BoujeeEnjinia1701/voidscope/cad/drawings/VDS-DWG-001.pdf

CONCEPT, NOT FOR FABRICATION | VoidScope · github.com/BoujeeEnjinia1701/voidscope

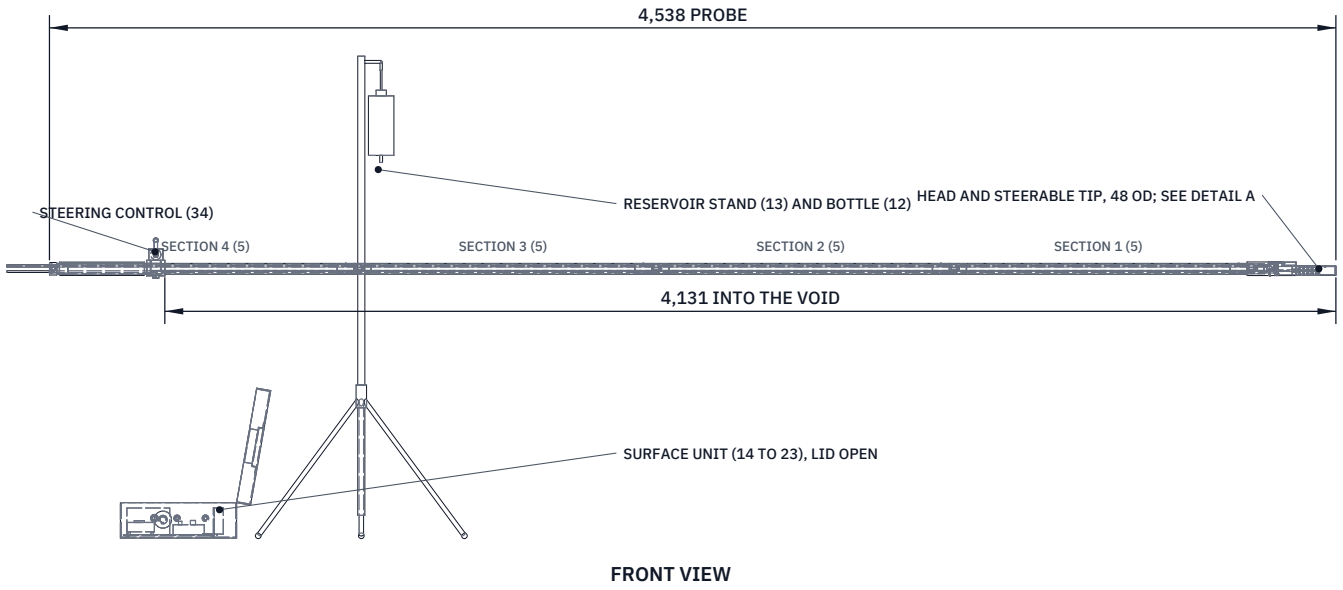
[picture p47: figure]
FRONT VIEW; 4,538 PROBE; 4,131 INTO THE VOID; STEERING CONTROL (34); SECTION 4 (5); SECTION 3 (5); SECTION 2 (5); SECTION 1 (5); SURFACE UNIT (14 TO 23), LID OPEN; RESERVOIR STAND (13) AND BOTTLE (12)

Scale 1:25; looking at the front (along +Y)

TOP VIEW
Scale 1:25; looking down (along -Z)

RIGHT VIEW
Scale 1:25; looking at the right side (along -X)

4688

1098 1702

HEAD AND STEERABLE TIP, 48 OD; SEE DETAIL A

TAIL CAP AND AIR INLET (7); GRIP (8)

OPERATOR STANDS BEHIND THE TAIL CAP (-X); TIP POINTS +X

ISOMETRIC VIEW
Not to scale; seen from the front right and above, about 30 deg elevation

DETAIL A: HEAD AND STEERABLE TIP
Scale 1:2.5; plan from above, tip to the right, straight; bends 90 deg each way in this plane

MAIN DIMENSIONS AND INTERFACES (MM)
Probe 4,538 long; working length 4,131; axis 950 above ground as held Rod: 4 sections 38.1 x 1.47 6061-T6 tube, 1,050 long
Couplers 34.93 x 2.11 x 120, 60 bonded and pinned; snap button Head 48 OD at most, tip straight; passes a 51 mm core hole (R1) Collar: socket, plenum, 6 x 5 outlets, speaker, water exit
Nose: base link 6.5 below the axis; bite valve on top
Tip: 5 joints, 90 deg each way; 140 long; 29 mm IP68 camera Steering: lever and drum on section 4, two wires in housings Air: rod bore is the duct; inlet barb on the tail cap
Water: 4 x 2.5 tube inside an 8 x 6 PTFE guide
Case 410 x 330 x 175; lid opened 100 deg
Third-angle; front view from -Y; (n) = BOM line
REV | DESCRIPTION | DATE | BY
P1 | Preliminary GA for TRL 3 (from cad/src/model.py) | 2026-10-03 | AC
P2 | VDS-DDR-002: design for construction | 2026-10-03 | AC
P3 | VDS-DDR-003: steerable camera tip and steering control | 2026-10-03 | AC
VOIDSCOPE | github.com/BoujeeEnjinia1701/voidscope

## Rubble void search probe and surface unit: general arrangement

DRAWING NO.
VDS-DWG-001

REV
P3

SHEET
1 of 1

SIZE

## ANSI B

SCALE
1:25

UNITS
mm
PROJECTION | DATE
2026-10-03

DRAWN
Amish Chadha

MATERIAL / NOTES
6061-T6 aluminium tube and bar; bought parts per bom/bom.csv. PRELIMINARY, NOT FOR FABRICATION
Licensed CERN-OHL-S-2.0 · Design Molecule Lab · designmolecule.com | Generated from cad/src; do not edit by hand
