BoujeeEnjinia1701/voidscope/cad/drawings/VDS-DWG-101.pdf

### BUILD PLAN SKETCH, PLAN NOT YET BUILT VoidScope · github.com/BoujeeEnjinia1701/voidscope

FRONT VIEW
Scale 1:5; looking at the front (along +Y)

TOP VIEW
Scale 1:5; looking down (along -Z)

RIGHT VIEW
Scale 1:5; looking at the right side (along -X)

1050

38 38

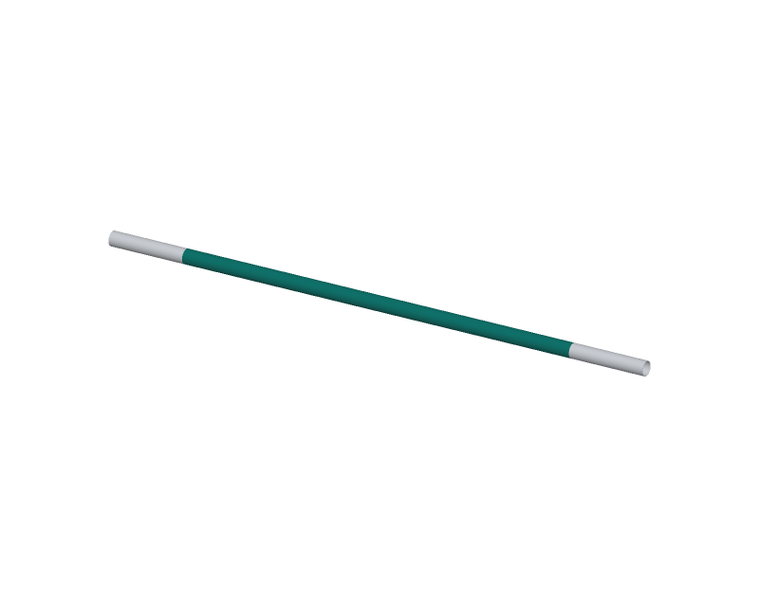
[picture p48: figure]

WHERE IT GOES
This part in colour, its neighbours in grey

HOW TO MAKE IT AND HOW IT FITS
Make four. Cut 1,050 mm, square, from 38.1 x 1.47 mm tube. Deburr inside and out; the inside edge must not cut the cable. Scribe a straight line along the tube: the button line (+Y). Back end, sections 1 to 3: drill 8.5 mm on the button line,
30 mm from the end. This takes the next section's button.

Back end, section 4: no button hole; the tail cap pins go in 4.0 mm holes top and bottom, 20 mm from the end (step 2); two 4 mm housing holes on top, 10.5 mm off centre,
332 and 368 mm from the back end.
Front end: the coupler pin holes, 4.0 mm top and bottom 30 mm from the end, are drilled through with the coupler fitted.
Depth marks every 100 mm from the tip, section number at each end, paint marker under clear heat-shrink.
Check: the next coupler slides in by hand with no rock.
REV | DESCRIPTION | DATE | BY
P1 | Making sketch for the prototype build plan | 2026-10-03 | AC
P2 | VDS-DDR-003: steerable camera tip | 2026-10-03 | AC
VOIDSCOPE | github.com/BoujeeEnjinia1701/voidscope

## VoidScope rod section (make 4): making sketch

DRAWING NO.
VDS-DWG-101

REV
P2

SHEET
1 of 1

SIZE

## ANSI B

SCALE
1:5

UNITS
mm
PROJECTION | DATE
2026-10-03

DRAWN
Amish Chadha

MATERIAL / NOTES
6061-T6 drawn tube 38.1 x 1.47 mm (1.5 x 0.058 in)
Licensed CERN-OHL-S-2.0 · Design Molecule Lab · designmolecule.com | Generated from cad/src; do not edit by hand
