BoujeeEnjinia1701/voidscope/cad/drawings/VDS-DWG-102.pdf

### BUILD PLAN SKETCH, PLAN NOT YET BUILT VoidScope · github.com/BoujeeEnjinia1701/voidscope

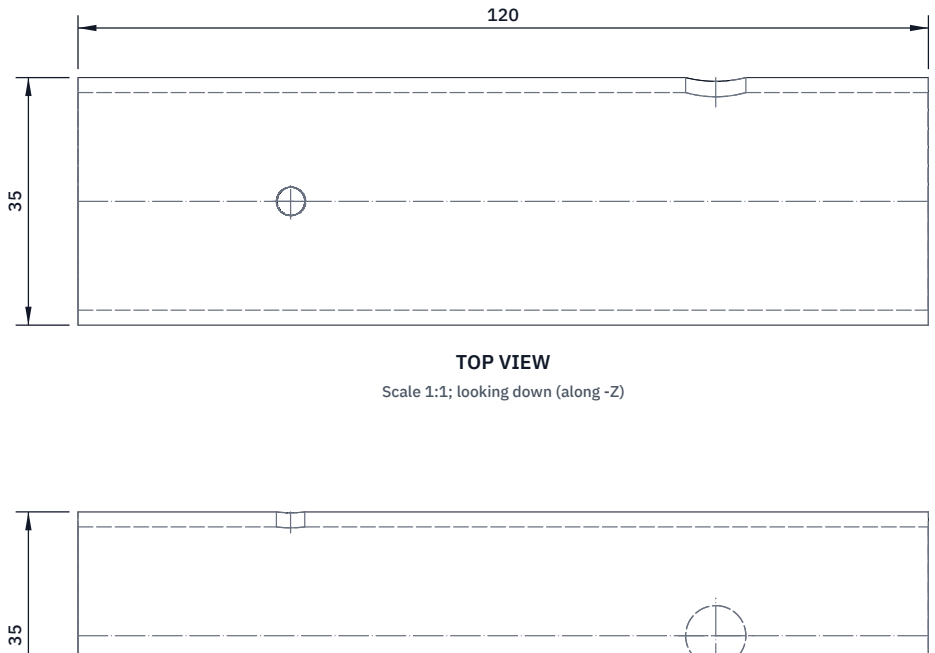
[picture p49: figure]
TOP VIEW; Scale 1:1; looking down (along -Z)

FRONT VIEW
Scale 1:1; looking at the front (along +Y)

RIGHT VIEW
Scale 1:1; looking at the right side (along -X)

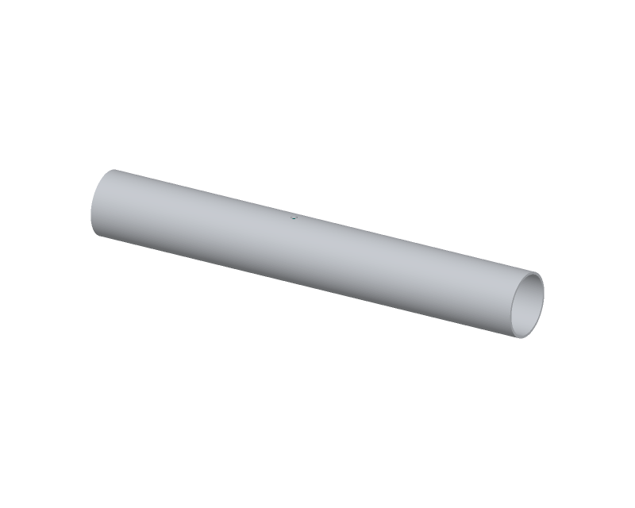
[picture p50: figure]

WHERE IT GOES
This part in colour, its neighbours in grey

HOW TO MAKE IT AND HOW IT FITS
Make four. Cut 120 mm from 34.93 x 2.11 mm tube; deburr. Chamfer the outside of one end 1 mm x 45 deg: the free end. Drill 8.5 mm for the snap button 30 mm from the free end. Fit the V-spring button from inside, button out through
the hole. Spring legs lie flat across the bore (top to
bottom stays clear for the cable and guide tube).
Bond: the plain end goes 60 mm into the section's front end with structural epoxy, button on the section's button line. Drill 4.0 mm through tube and coupler, top and bottom, 30 mm from the section end; press in the pins flush both sides.
Fit: 0.11 mm a side in the next tube; it must slide freely. Check: pull hard by hand; nothing moves; button pops fully.
REV | DESCRIPTION | DATE | BY
P1 | Making sketch for the prototype build plan | 2026-10-03 | AC
VOIDSCOPE | github.com/BoujeeEnjinia1701/voidscope

## VoidScope coupler (make 4): making sketch

DRAWING NO.
VDS-DWG-102

REV
P1

SHEET
1 of 1

SIZE

## ANSI B

SCALE
1:1

UNITS
mm
PROJECTION | DATE
2026-10-03

DRAWN
Amish Chadha

MATERIAL / NOTES
6061-T6 drawn tube 34.93 x 2.11 mm (1.375 x 0.083 in)
Licensed CERN-OHL-S-2.0 · Design Molecule Lab · designmolecule.com | Generated from cad/src; do not edit by hand
