BoujeeEnjinia1701/voidscope/cad/drawings/VDS-DWG-103.pdf

### BUILD PLAN SKETCH, PLAN NOT YET BUILT VoidScope · github.com/BoujeeEnjinia1701/voidscope

FRONT VIEW
Scale 1:1; looking at the front (along +Y)

TOP VIEW
Scale 1:1; looking down (along -Z)

RIGHT VIEW
Scale 1:1; looking at the right side (along -X)

75

48 48

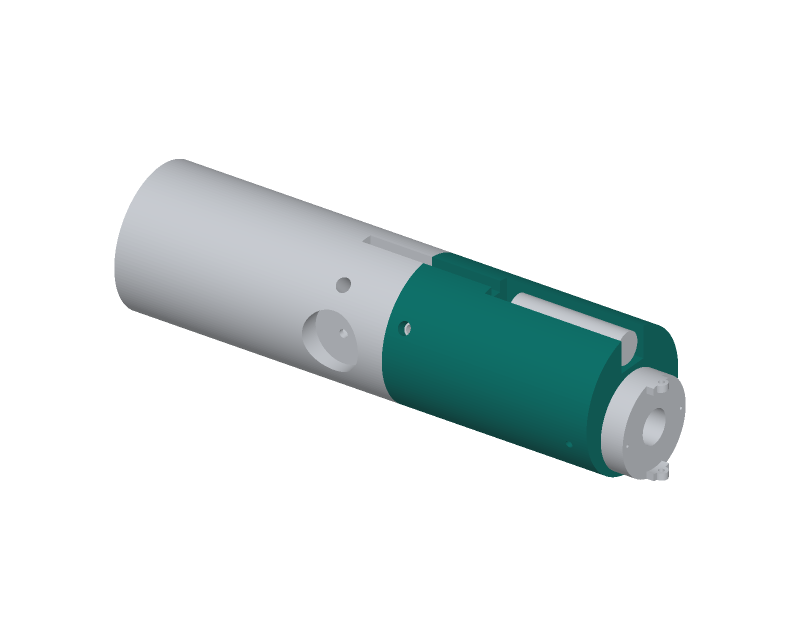
[picture p51: figure]

WHERE IT GOES
This part in colour, its neighbours in grey

HOW TO MAKE IT AND HOW IT FITS
Lathe: face and turn to 48 mm outside, 75 mm long.
Back end: bore 40.2 mm, 12 mm deep, for the collar spigot. Offset the work 6.5 mm (4-jaw chuck): bore 29.3 mm from 12 mm right through the front, for the base link of the steerable tip. Thinnest wall 2.85 mm, at the bottom.
Mill or saw and file on top: pocket 11.5 mm wide, floor
12 mm above the axis, 50 mm back from the front face. Groove on top 4.5 mm wide, floor 20 mm above the axis, from the back face to the pocket (breaks into the bore). Three 4.5 mm holes 6 mm from the back face, at 30, 150 and 270 deg from the side; countersink for M4.
Two M3 tapped holes, 7 mm from the front, either side on the bore's centre height, for the base link grub screws. Break edges 0.5 mm. Check: base link spigot slides in.
REV | DESCRIPTION | DATE | BY
P1 | Making sketch for the prototype build plan | 2026-10-03 | AC
P2 | VDS-DDR-003: steerable camera tip | 2026-10-03 | AC
VOIDSCOPE | github.com/BoujeeEnjinia1701/voidscope

## VoidScope nose: making sketch

DRAWING NO.
VDS-DWG-103

REV
P2

SHEET
1 of 1

SIZE

## ANSI B

SCALE
1:1

UNITS
mm
PROJECTION | DATE
2026-10-03

DRAWN
Amish Chadha

MATERIAL / NOTES
6061-T6 round bar 50 mm, 80 mm long
Licensed CERN-OHL-S-2.0 · Design Molecule Lab · designmolecule.com | Generated from cad/src; do not edit by hand
