BoujeeEnjinia1701/voidscope/cad/drawings/VDS-DWG-104.pdf

### BUILD PLAN SKETCH, PLAN NOT YET BUILT VoidScope · github.com/BoujeeEnjinia1701/voidscope

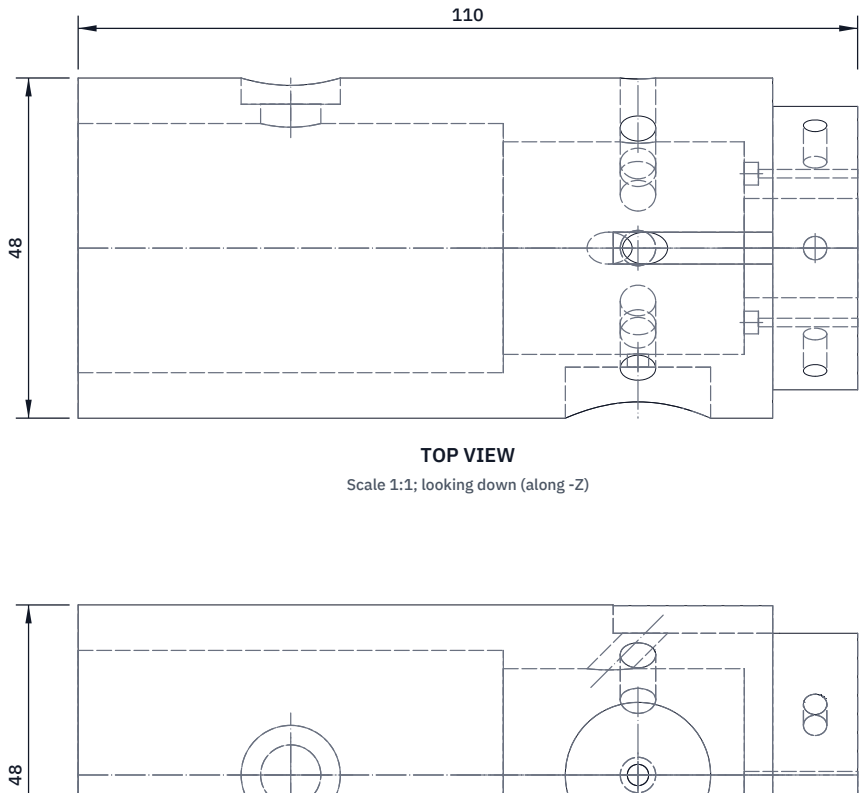
[picture p52: figure]
TOP VIEW; Scale 1:1; looking down (along -Z)
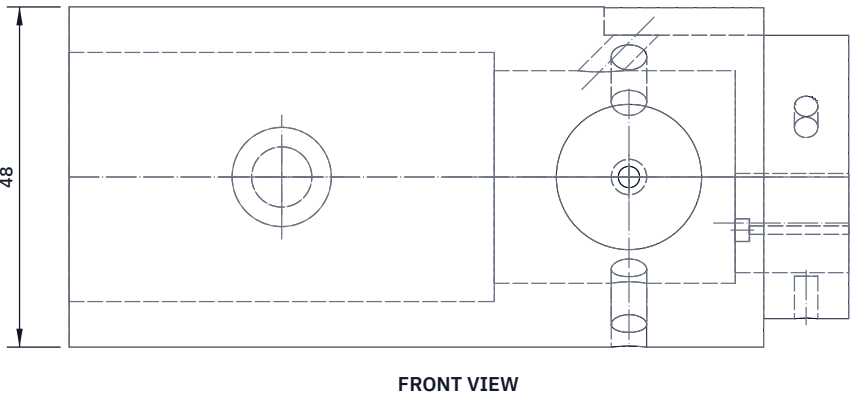
[picture p53: figure]
FRONT VIEW

Scale 1:1; looking at the front (along +Y)

RIGHT VIEW
Scale 1:1; looking at the right side (along -X)

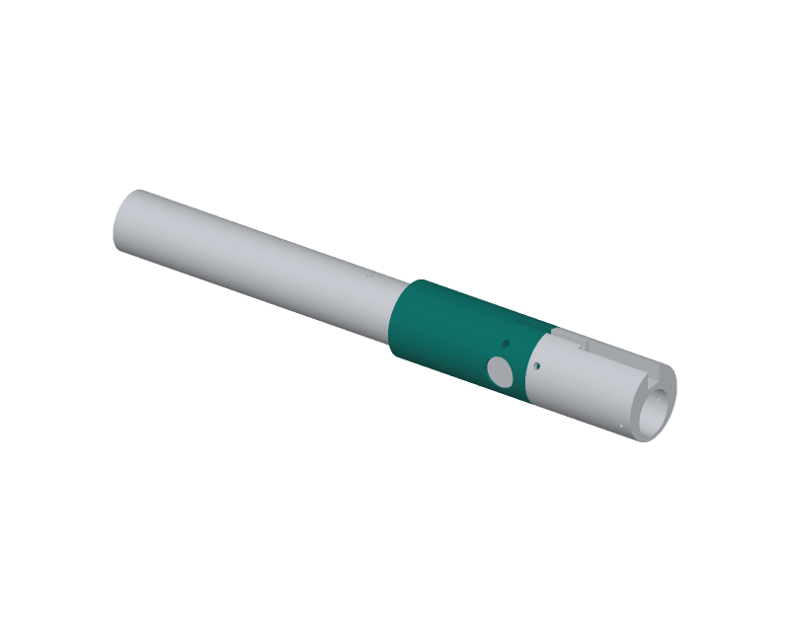
[picture p54: figure]

WHERE IT GOES
This part in colour, its neighbours in grey

HOW TO MAKE IT AND HOW IT FITS
Lathe: 48 mm outside x 98 mm, then a 40 mm spigot 12 long. Back: bore 35.16 mm, 60 deep (a coupler must slide in).
Bore 30 mm from 60 to 94 mm: the air plenum; 4 mm front wall. Spigot: 14 mm bore 6.5 mm below the axis, through, for the cable grommet. Tap three M4 holes 6 mm deep, 4 from its end. Button hole 8.5 mm on the button line, 30 mm from the back; spotface 14 mm down to 20.3 mm from the axis.
Six 5 mm outlets 79 mm from the back face, at 0, 45, 135, 240, 270 and 300 deg from the button line toward the top. Steering: two 3.2 mm stops 2 deep in the plenum side of the front wall, 10.5 mm each side, 7.5 below the axis; 1.2 mm wire holes on through the spigot.
Speaker pocket on the far side: 20.5 mm, flat floor 16.8 mm from the axis, 79 mm back; 3 mm wire hole into the plenum. Water exit 4.5 mm at 45 deg on top, axis crossing 12 mm above the axis 72 mm from the back; groove 4.5 x 4 on top. Check: coupler, nose, speaker fit; blow through outlets.
REV | DESCRIPTION | DATE | BY
P1 | Making sketch for the prototype build plan | 2026-10-03 | AC
P2 | VDS-DDR-003: steerable camera tip | 2026-10-03 | AC
VOIDSCOPE | github.com/BoujeeEnjinia1701/voidscope

## VoidScope collar: making sketch

DRAWING NO.
VDS-DWG-104

REV
P2

SHEET
1 of 1

SIZE

## ANSI B

SCALE
1:1

UNITS
mm
PROJECTION | DATE
2026-10-03

DRAWN
Amish Chadha

MATERIAL / NOTES
6061-T6 round bar 50 mm, 115 mm long
Licensed CERN-OHL-S-2.0 · Design Molecule Lab · designmolecule.com | Generated from cad/src; do not edit by hand
