BoujeeEnjinia1701/voidscope/cad/drawings/VDS-DWG-105.pdf

### BUILD PLAN SKETCH, PLAN NOT YET BUILT VoidScope · github.com/BoujeeEnjinia1701/voidscope

FRONT VIEW
Scale 1:1; looking at the front (along +Y)

TOP VIEW
Scale 1:1; looking down (along -Z)

RIGHT VIEW
Scale 1:1; looking at the right side (along -X)

65

44 44

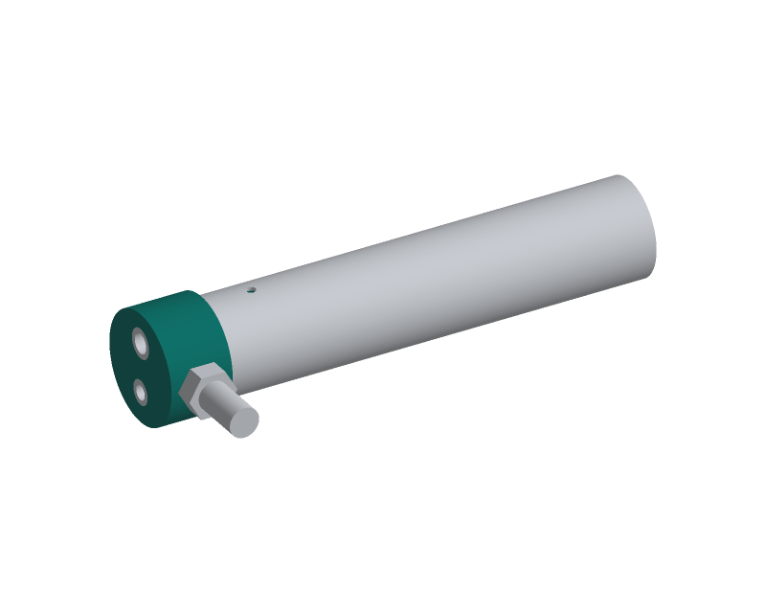
[picture p55: figure]

WHERE IT GOES
This part in colour, its neighbours in grey

HOW TO MAKE IT AND HOW IT FITS
Lathe: flange 44 mm outside x 25 mm; plug 35.0 mm x 40 mm (0.08 mm a side in the rod: bonded, not a slide fit).
Bore 30 mm from the plug end to 8 mm from the back face. End wall: 10 mm hole 10 mm below the axis (cable) and
12 mm hole 10 mm above it (guide tube); deburr; grommets. Side of the flange, away from the button line: drill and
tap 1/4 BSP 12.5 mm from the back face into the bore. Pins: drill 4.0 mm top and bottom through rod and plug
20 mm in front of the flange after bonding (step 2). Check: plug enters the rod fully; barb seals with tape.
REV | DESCRIPTION | DATE | BY
P1 | Making sketch for the prototype build plan | 2026-10-03 | AC
VOIDSCOPE | github.com/BoujeeEnjinia1701/voidscope

## VoidScope tail cap: making sketch

DRAWING NO.
VDS-DWG-105

REV
P1

SHEET
1 of 1

SIZE

## ANSI B

SCALE
1:1

UNITS
mm
PROJECTION | DATE
2026-10-03

DRAWN
Amish Chadha

MATERIAL / NOTES
6061-T6 round bar 50 mm, 70 mm long
Licensed CERN-OHL-S-2.0 · Design Molecule Lab · designmolecule.com | Generated from cad/src; do not edit by hand
