BoujeeEnjinia1701/voidscope/cad/drawings/VDS-DWG-106.pdf

### BUILD PLAN SKETCH, PLAN NOT YET BUILT VoidScope · github.com/BoujeeEnjinia1701/voidscope

FRONT VIEW
Scale 1:5; looking at the front (along +Y)

TOP VIEW
Scale 1:5; looking down (along -Z)

RIGHT VIEW
Scale 1:5; looking at the right side (along -X)

330

300 3

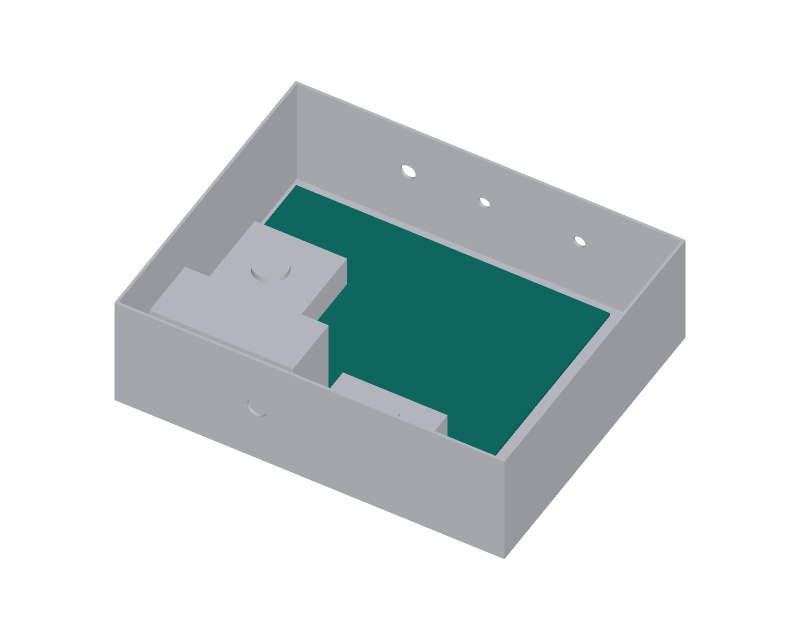
[picture p56: figure]

WHERE IT GOES
This part in colour, its neighbours in grey

HOW TO MAKE IT AND HOW IT FITS
Cut 330 x 300 mm from 3 mm sheet; round corners 5 mm. Corner holes 5.5 mm, 15 mm in from each edge: the four spacers and M5 screws through the case floor.
Mark the parts from the corner nearest the case's -X, -Y corner: battery at 12, 12 (151 x 65); strap slots 4 x 25 mm each side of it; blower at 12, 110 on four standoffs; modules tray at 175, 12; flow meter angle at 280, 230. Drill each fixing to suit the part as bought (M3 or M4). Deburr; no sharp edge near the battery leads.
Check: lay every part on the plate before drilling.
REV | DESCRIPTION | DATE | BY
P1 | Making sketch for the prototype build plan | 2026-10-03 | AC
VOIDSCOPE | github.com/BoujeeEnjinia1701/voidscope

## VoidScope equipment plate: making sketch

DRAWING NO.
VDS-DWG-106

REV
P1

SHEET
1 of 1

SIZE

## ANSI B

SCALE
1:5

UNITS
mm
PROJECTION | DATE
2026-10-03

DRAWN
Amish Chadha

MATERIAL / NOTES
5052 aluminium sheet 3 mm
Licensed CERN-OHL-S-2.0 · Design Molecule Lab · designmolecule.com | Generated from cad/src; do not edit by hand
