BoujeeEnjinia1701/voidscope/cad/drawings/VDS-DWG-108.pdf

### BUILD PLAN SKETCH, PLAN NOT YET BUILT VoidScope · github.com/BoujeeEnjinia1701/voidscope

FRONT VIEW
Scale 1:5; looking at the front (along +Y)

TOP VIEW
Scale 1:5; looking down (along -Z)

RIGHT VIEW
Scale 1:5; looking at the right side (along -X)

410

330 125

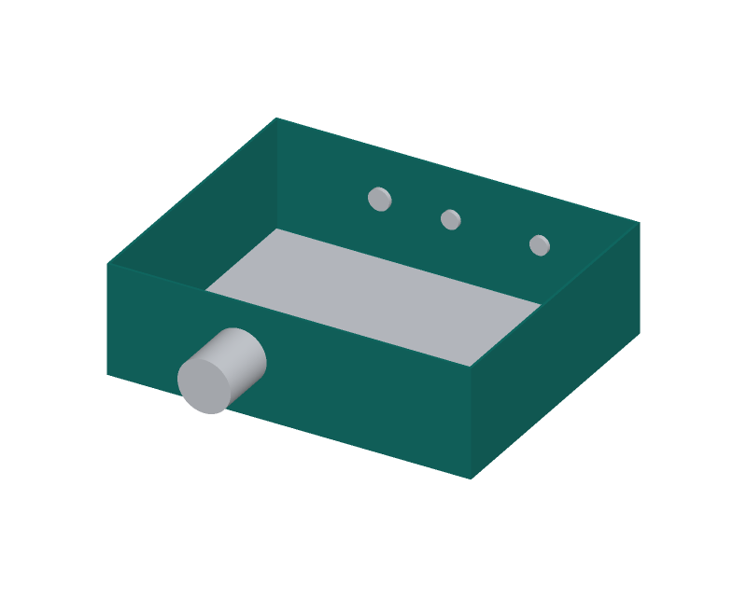
[picture p57: figure]

WHERE IT GOES
This part in colour, its neighbours in grey

HOW TO MAKE IT AND HOW IT FITS
Bought case 410 x 330 x 175 mm; drill the base only as here. Wall toward the probe (the +Y long side), 70 mm up from the floor outside: 16 mm for the camera socket 120 mm from the left end; 12 mm for the headset socket at 200 mm; 12.5 mm for the air outlet bulkhead at 300 mm.
Opposite wall: 21 mm for the intake filter, 150 mm from the left end, 65 mm up.
Floor: four 5.5 mm holes matching the plate's corner holes. Lid: four 5.5 mm holes for the monitor bracket feet.
Use a step drill, slow; deburr; every hole gets its seal. Check: the case still closes and latches.
REV | DESCRIPTION | DATE | BY
P1 | Making sketch for the prototype build plan | 2026-10-03 | AC
VOIDSCOPE | github.com/BoujeeEnjinia1701/voidscope

## VoidScope surface unit case: drilling sketch

DRAWING NO.
VDS-DWG-108

REV
P1

SHEET
1 of 1

SIZE

## ANSI B

SCALE
1:5

UNITS
mm
PROJECTION | DATE
2026-10-03

DRAWN
Amish Chadha

MATERIAL / NOTES
Bought IP67 case, polypropylene
Licensed CERN-OHL-S-2.0 · Design Molecule Lab · designmolecule.com | Generated from cad/src; do not edit by hand
