BoujeeEnjinia1701/voidscope/cad/drawings/VDS-DWG-110.pdf

### BUILD PLAN SKETCH, PLAN NOT YET BUILT VoidScope · github.com/BoujeeEnjinia1701/voidscope

FRONT VIEW
Scale 2:1; looking at the front (along +Y)

TOP VIEW
Scale 2:1; looking down (along -Z)

RIGHT VIEW
Scale 2:1; looking at the right side (along -X)

20

33 33

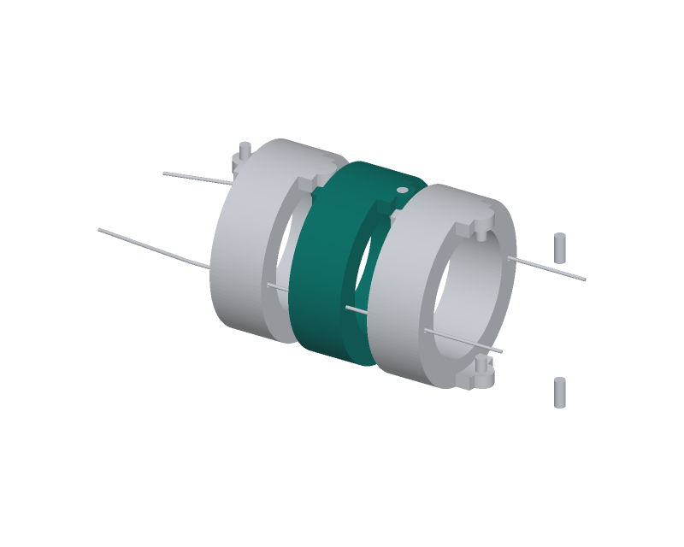
[picture p58: figure]

WHERE IT GOES
This part in colour, its neighbours in grey

HOW TO MAKE IT AND HOW IT FITS
Make four by laser sintering in PA12 from the model; any online print service. No supports needed.
Body 33 mm outside, 23 mm bore, 10 mm long. Back: inner lugs 8 mm wide, top and bottom, 11.5 to 13.9 mm from the centre. Front: outer lugs, 14.1 to 16.5 mm. Lug ends are rounded about the pin.
Pin holes 2.0 mm (ream after printing), 2.6 mm from each lug's root face, top and bottom.
Wire holes 1.2 mm on the two sides, 14 mm from the centre; run a 1.2 mm drill through each.
The faces close at 18 deg: that is the joint's stop.
Check: two links pin together and swing 18 deg each way.
REV | DESCRIPTION | DATE | BY
P1 | Making sketch for the prototype build plan | 2026-10-03 | AC
VOIDSCOPE | github.com/BoujeeEnjinia1701/voidscope

## VoidScope bending link (make 4): making sketch

DRAWING NO.
VDS-DWG-110

REV
P1

SHEET
1 of 1

SIZE

## ANSI B

SCALE
2:1

UNITS
mm
PROJECTION | DATE
2026-10-03

DRAWN
Amish Chadha

MATERIAL / NOTES
PA12 nylon, laser sintered (SLS)
Licensed CERN-OHL-S-2.0 · Design Molecule Lab · designmolecule.com | Generated from cad/src; do not edit by hand
