BoujeeEnjinia1701/voidscope/cad/drawings/VDS-DWG-111.pdf

### BUILD PLAN SKETCH, PLAN NOT YET BUILT VoidScope · github.com/BoujeeEnjinia1701/voidscope

FRONT VIEW
Scale 2:1; looking at the front (along +Y)

TOP VIEW
Scale 2:1; looking down (along -Z)

RIGHT VIEW
Scale 2:1; looking at the right side (along -X)

27

33 33

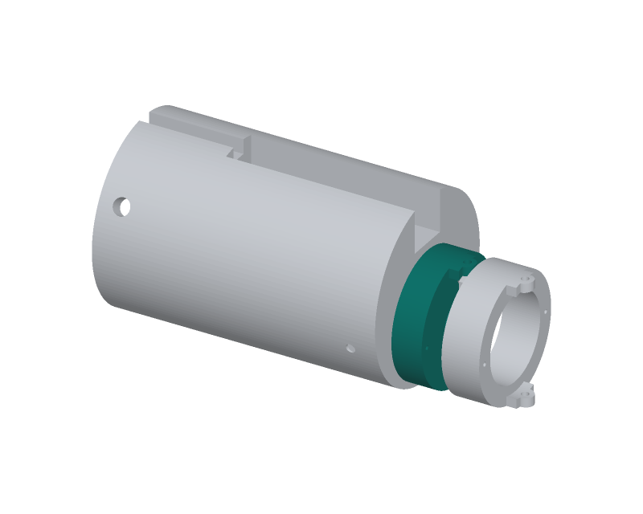
[picture p59: figure]

WHERE IT GOES
This part in colour, its neighbours in grey

HOW TO MAKE IT AND HOW IT FITS
Lathe: 29.25 mm spigot 14 mm long, 33 mm flange 8 mm, 12 mm bore through. The spigot is a close slide fit in
the nose's 29.3 mm bore.
Front: leave a 4.9 mm stub at 33 mm outside; mill it
away to two outer lugs, 8 mm wide, top and bottom, outside 14.1 mm from the centre; round the lug ends. Drill 2.0 mm pin holes 2.6 mm ahead of the flange face. Wire holes 1.2 mm, drilled on a slant: from 10.5 mm out
and 1 mm low at the back face to 14 mm out on the
centre line at the flange front (a drill jig helps).
Two dimples 1.5 mm deep, 7 mm from the spigot's front end, on the sides, for the M3 grub screws in the nose.
REV | DESCRIPTION | DATE | BY
P1 | Making sketch for the prototype build plan | 2026-10-03 | AC
VOIDSCOPE | github.com/BoujeeEnjinia1701/voidscope

## VoidScope base link: making sketch

DRAWING NO.
VDS-DWG-111

REV
P1

SHEET
1 of 1

SIZE

## ANSI B

SCALE
2:1

UNITS
mm
PROJECTION | DATE
2026-10-03

DRAWN
Amish Chadha

MATERIAL / NOTES
6061-T6 round bar 35 mm, 25 mm long
Licensed CERN-OHL-S-2.0 · Design Molecule Lab · designmolecule.com | Generated from cad/src; do not edit by hand
