BoujeeEnjinia1701/voidscope/cad/drawings/VDS-DWG-112.pdf

### BUILD PLAN SKETCH, PLAN NOT YET BUILT VoidScope · github.com/BoujeeEnjinia1701/voidscope

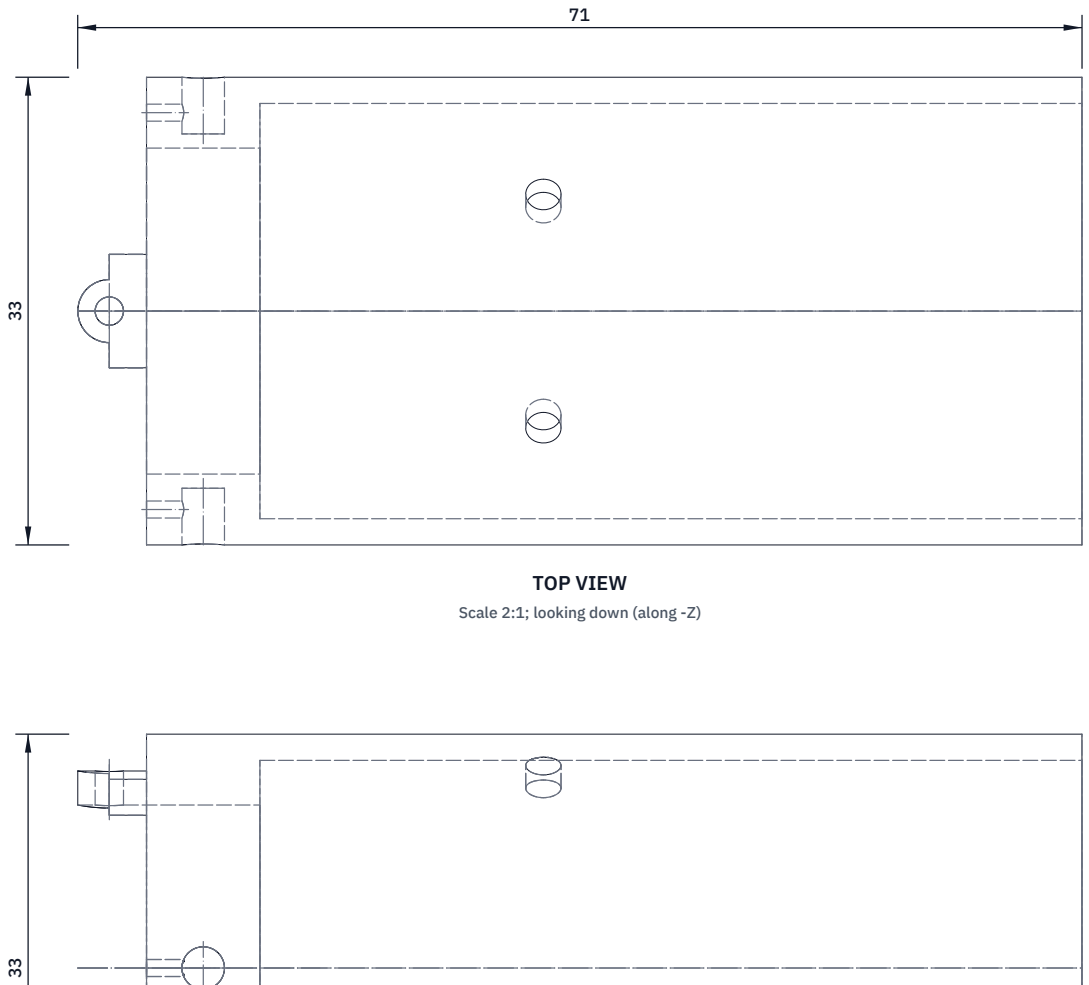
[picture p60: figure]
TOP VIEW; Scale 2:1; looking down (along -Z)
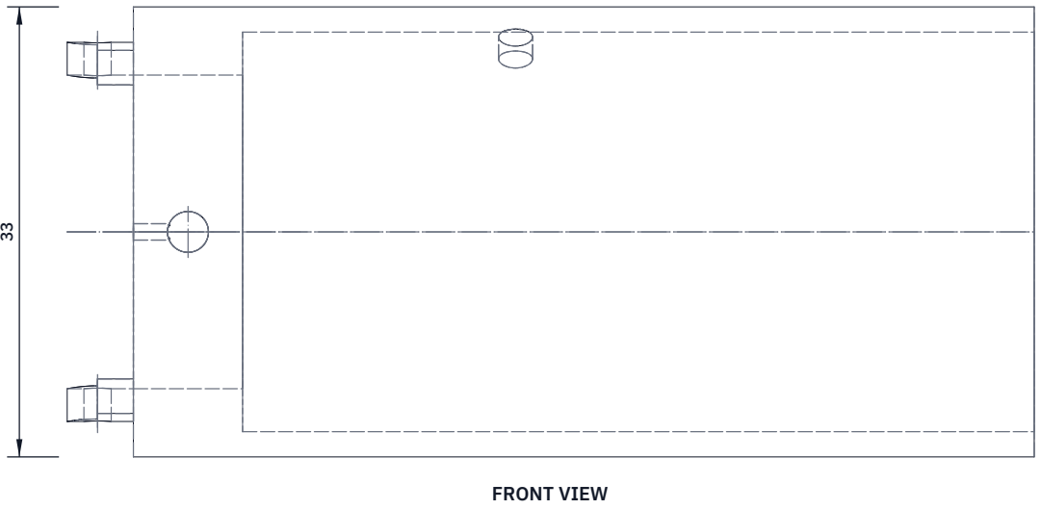
[picture p61: figure]
FRONT VIEW

Scale 2:1; looking at the front (along +Y)

RIGHT VIEW
Scale 2:1; looking at the right side (along -X)

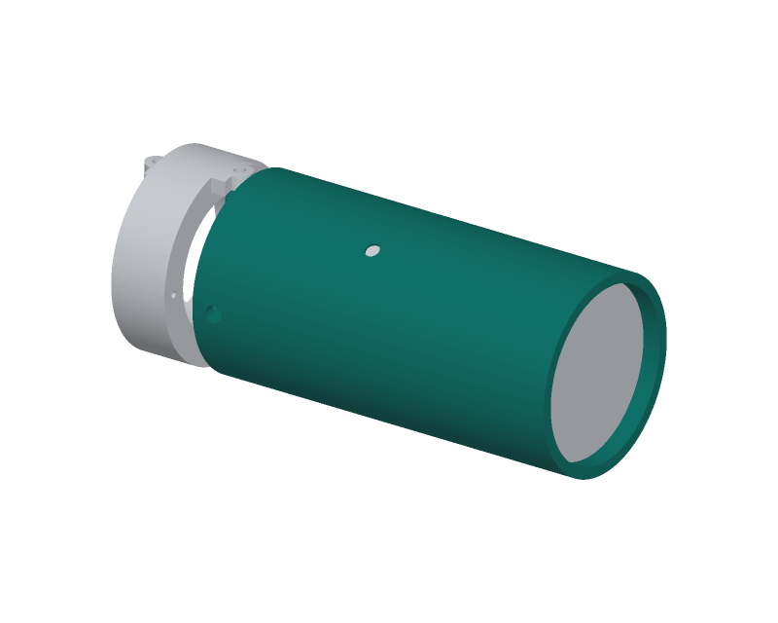
[picture p62: figure]

WHERE IT GOES
This part in colour, its neighbours in grey

HOW TO MAKE IT AND HOW IT FITS
Lathe: 33 mm outside, 66 mm long. From the front, bore 29.3 mm 58 mm deep for the camera; the camera's face sits 3 mm back from the front edge. Bore 23 mm through the 8 mm back wall for the cable.
Back: leave a 4.9 mm stub; mill it to two inner lugs 8 mm wide, top and bottom, 11.5 to 13.9 mm from the centre; round the ends; drill 2.0 mm pin holes.
Wire anchors: 1.2 mm holes 14 mm out on the two sides, 4 mm deep, into 3 mm cross holes from the outside where the crimped ferrules sit.
Two M3 tapped holes, 20 mm from the camera's back, at 60 and 120 deg, for nylon-tipped grub screws.
REV | DESCRIPTION | DATE | BY
P1 | Making sketch for the prototype build plan | 2026-10-03 | AC
VOIDSCOPE | github.com/BoujeeEnjinia1701/voidscope

## VoidScope tip housing: making sketch

DRAWING NO.
VDS-DWG-112

REV
P1

SHEET
1 of 1

SIZE

## ANSI B

SCALE
2:1

UNITS
mm
PROJECTION | DATE
2026-10-03

DRAWN
Amish Chadha

MATERIAL / NOTES
6061-T6 round bar 35 mm, 75 mm long
Licensed CERN-OHL-S-2.0 · Design Molecule Lab · designmolecule.com | Generated from cad/src; do not edit by hand
