BoujeeEnjinia1701/voidscope/cad/drawings/VDS-DWG-113.pdf

### BUILD PLAN SKETCH, PLAN NOT YET BUILT VoidScope · github.com/BoujeeEnjinia1701/voidscope

FRONT VIEW
Scale 1:2; looking at the front (along +Y)

TOP VIEW
Scale 1:2; looking down (along -Z)

RIGHT VIEW
Scale 1:2; looking at the right side (along -X)

64

50 103

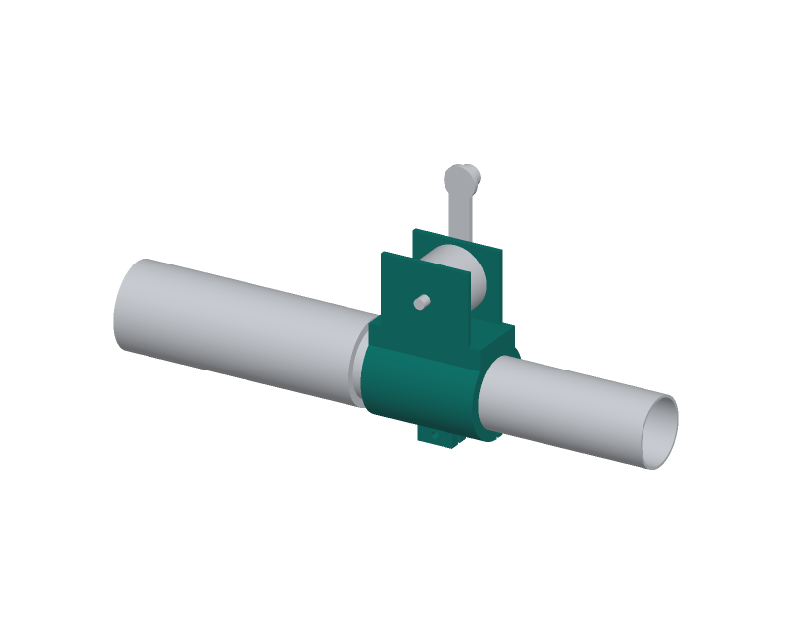
[picture p63: figure]

WHERE IT GOES
This part in colour, its neighbours in grey

HOW TO MAKE IT AND HOW IT FITS
Print in one piece in PA12 from the model: a collar that clamps section 4 (38.1 mm bore, 50 mm outside, 64 long), a pad on top and two cheeks 3 mm thick, 28 mm apart. Split along the bottom, 2 mm wide; two lugs with a 4.2 mm hole for the M4 clamp screw and nyloc nut.
Two 3.2 mm holes down through the pad, 10.5 mm either side of centre and 36 mm apart along the rod: the housings
stop 2 mm under the top; 1.2 mm holes on up for the wires. Shaft holes 6.2 mm through both cheeks, 50 mm above the rod's centre line; mark the centre detent on one cheek. Fit 8 mm ahead of the grip, holes over the rod's holes. Check: clamps firmly; drum turns freely between cheeks.
REV | DESCRIPTION | DATE | BY
P1 | Making sketch for the prototype build plan | 2026-10-03 | AC
VOIDSCOPE | github.com/BoujeeEnjinia1701/voidscope

## VoidScope steering control body: making sketch

DRAWING NO.
VDS-DWG-113

REV
P1

SHEET
1 of 1

SIZE

## ANSI B

SCALE
1:2

UNITS
mm
PROJECTION | DATE
2026-10-03

DRAWN
Amish Chadha

MATERIAL / NOTES
PA12 nylon, laser sintered (SLS)
Licensed CERN-OHL-S-2.0 · Design Molecule Lab · designmolecule.com | Generated from cad/src; do not edit by hand
