BoujeeEnjinia1701/voidscope/cad/drawings/VDS-DWG-114.pdf

### BUILD PLAN SKETCH, PLAN NOT YET BUILT VoidScope · github.com/BoujeeEnjinia1701/voidscope

FRONT VIEW
Scale 1:1; looking at the front (along +Y)

TOP VIEW
Scale 1:1; looking down (along -Z)

RIGHT VIEW
Scale 1:1; looking at the right side (along -X)

36

42 77

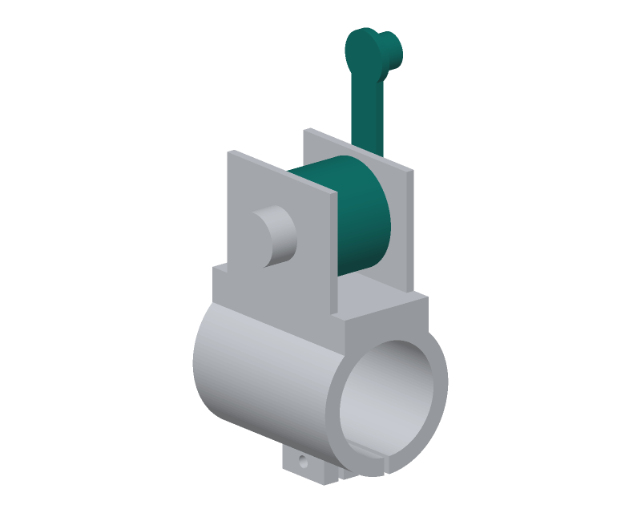
[picture p64: figure]

WHERE IT GOES
This part in colour, its neighbours in grey

HOW TO MAKE IT AND HOW IT FITS
Drum: turn 36 mm across, 27 mm long; 6 mm bore, a press fit on the shaft (or pin it). Two grooves 1 mm deep,
10.5 mm either side of the middle, one for each wire. Drill and tap M3 across each groove for a wire clamp screw with a washer; the wires lie on opposite sides. Lever: cut from 3 mm sheet, 12 mm wide, 59 mm from the shaft hole to the end, rounded; 6 mm hole; thumb peg
12 mm across riveted at the end.
Lever and drum are fixed to the shaft: the lever turns
71 deg for 90 deg at the tip, 35 deg for 45 deg.
Two stops on the cheek limit it to 71 deg each way. Check: from straight, each way, the tip bends 90 deg.
REV | DESCRIPTION | DATE | BY
P1 | Making sketch for the prototype build plan | 2026-10-03 | AC
VOIDSCOPE | github.com/BoujeeEnjinia1701/voidscope

## VoidScope steering drum and lever: making sketch

DRAWING NO.
VDS-DWG-114

REV
P1

SHEET
1 of 1

SIZE

## ANSI B

SCALE
1:1

UNITS
mm
PROJECTION | DATE
2026-10-03

DRAWN
Amish Chadha

MATERIAL / NOTES
6061-T6 bar 40 mm; 5052 sheet 3 mm
Licensed CERN-OHL-S-2.0 · Design Molecule Lab · designmolecule.com | Generated from cad/src; do not edit by hand
