BoujeeEnjinia1701/voidscope/cad/drawings/VDS-DWG-001.png

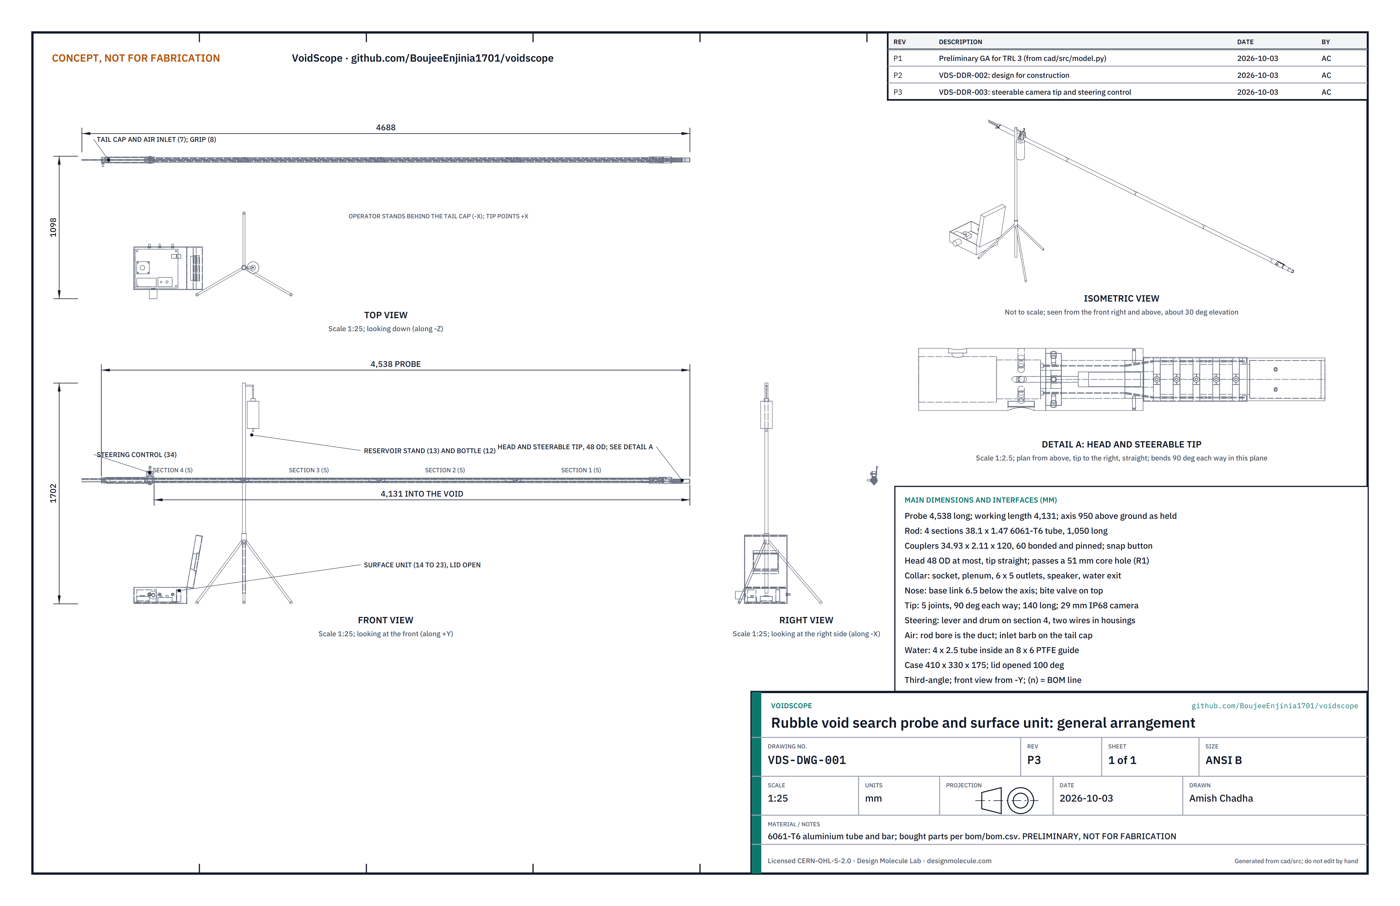
cad/drawings/VDS-DWG-001.png
