BoujeeEnjinia1701/voidscope/media/card.png

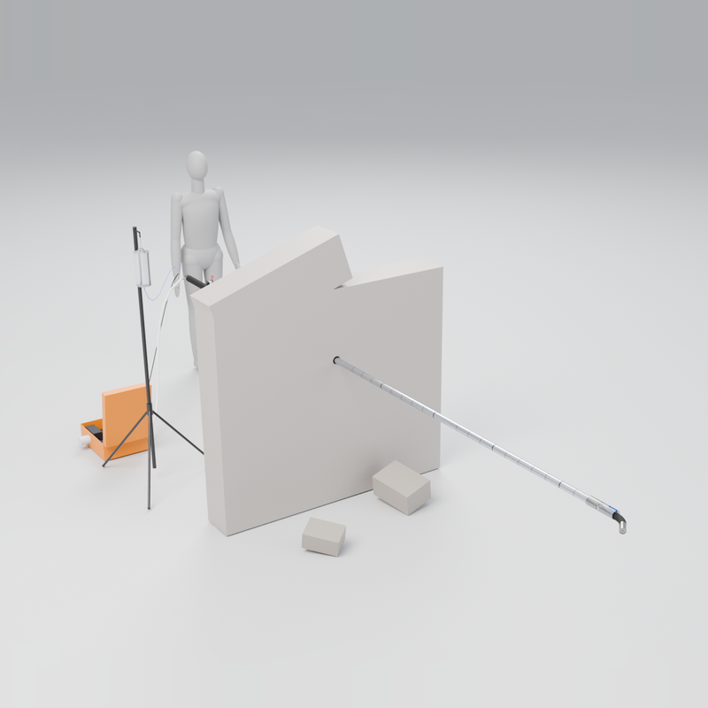
media/card.png
