BoujeeEnjinia1701/voidscope/media/cutaway.png

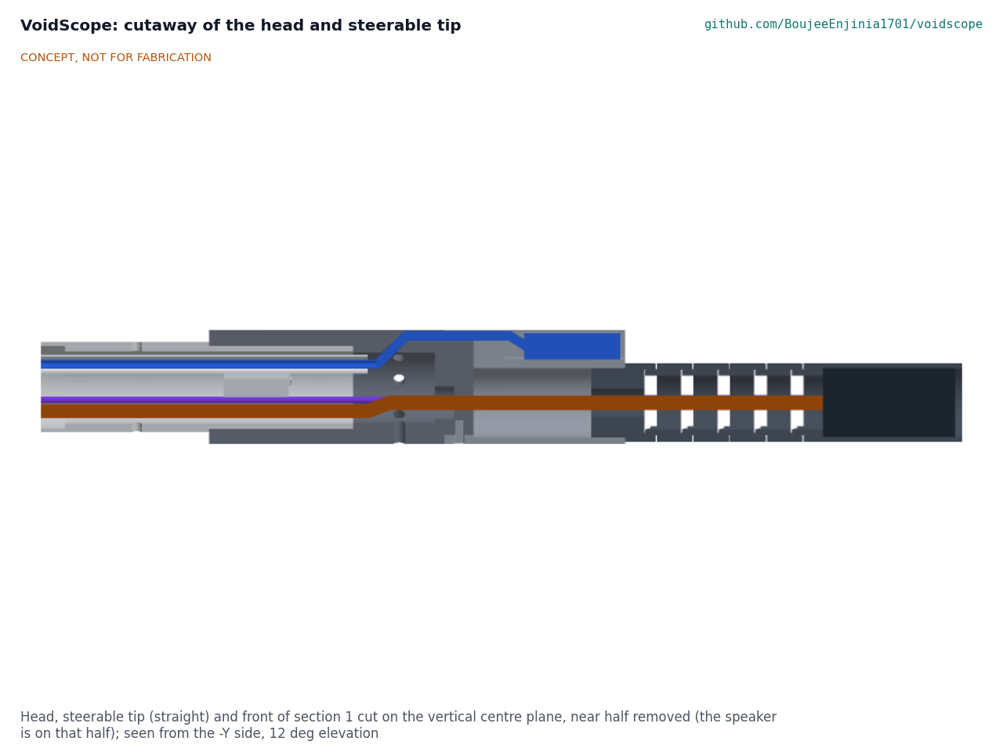
media/cutaway.png
