BoujeeEnjinia1701/voidscope/media/exploded.png

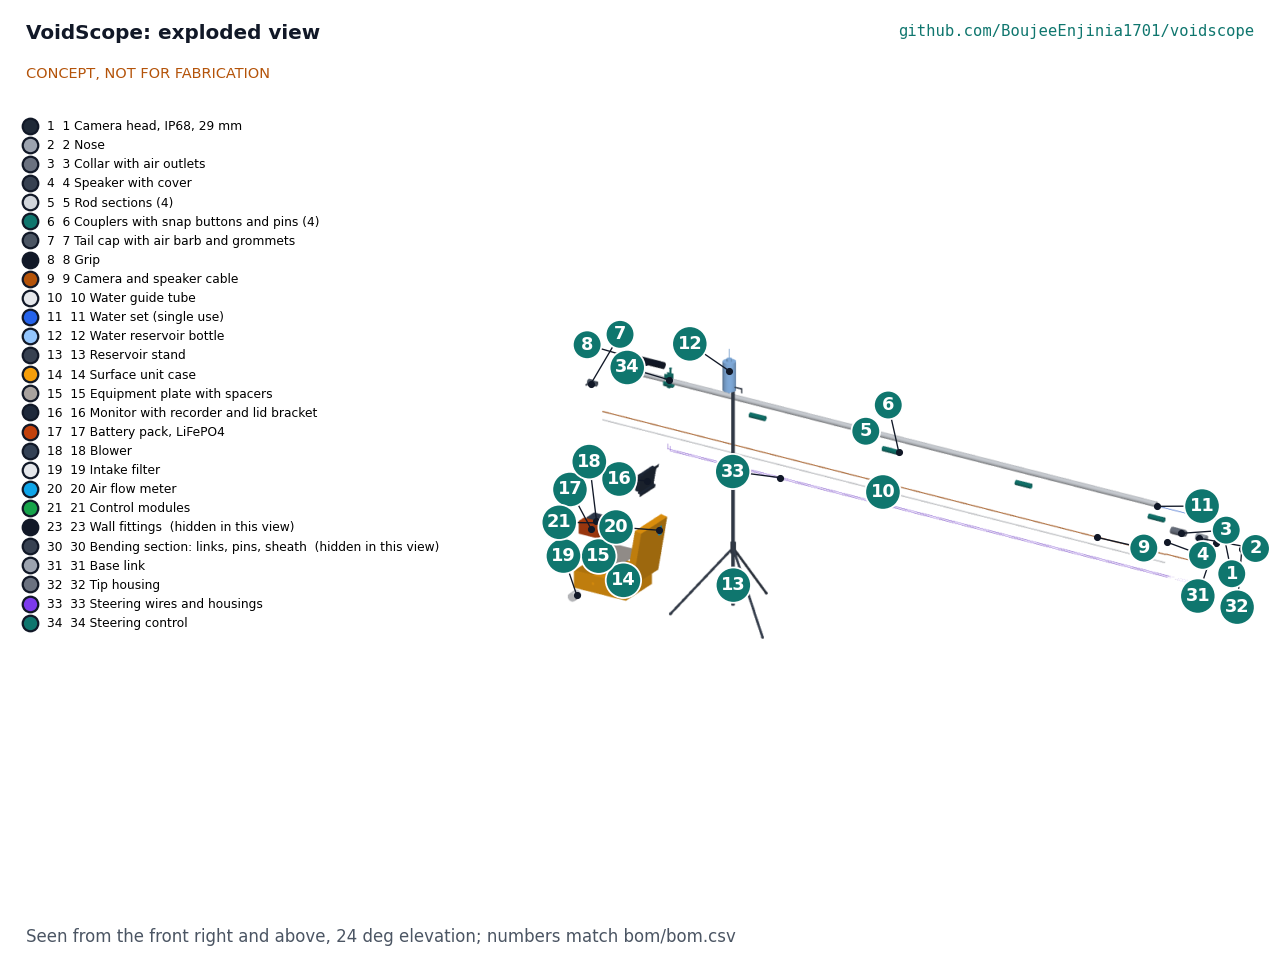
media/exploded.png
