BoujeeEnjinia1701/voidscope/media/render-detail.png

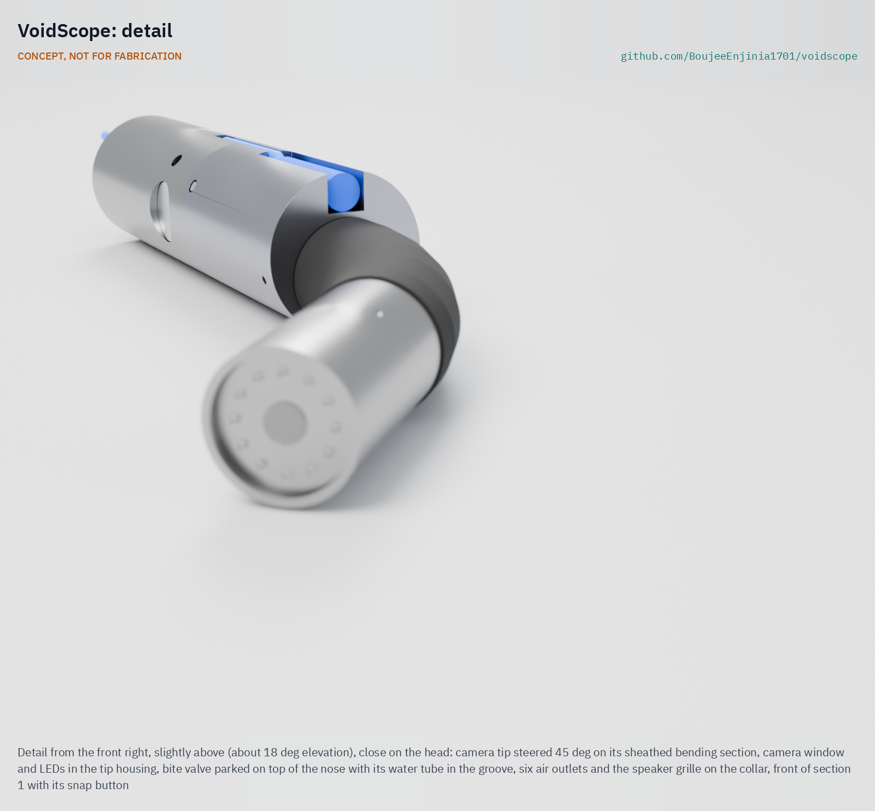
media/render-detail.png
