BoujeeEnjinia1701/voidscope/media/render-exploded.png

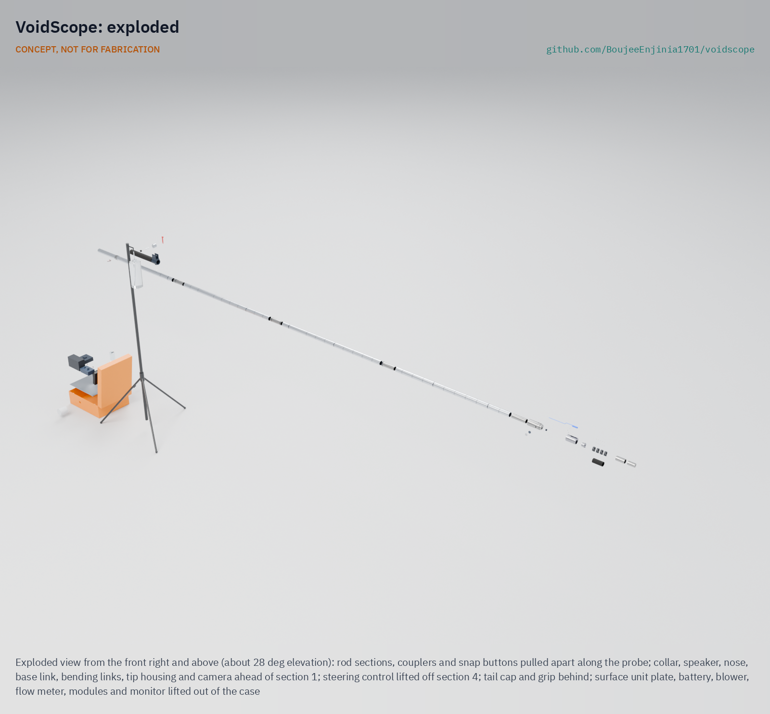
media/render-exploded.png
