BoujeeEnjinia1701/voidscope/media/social-preview.png

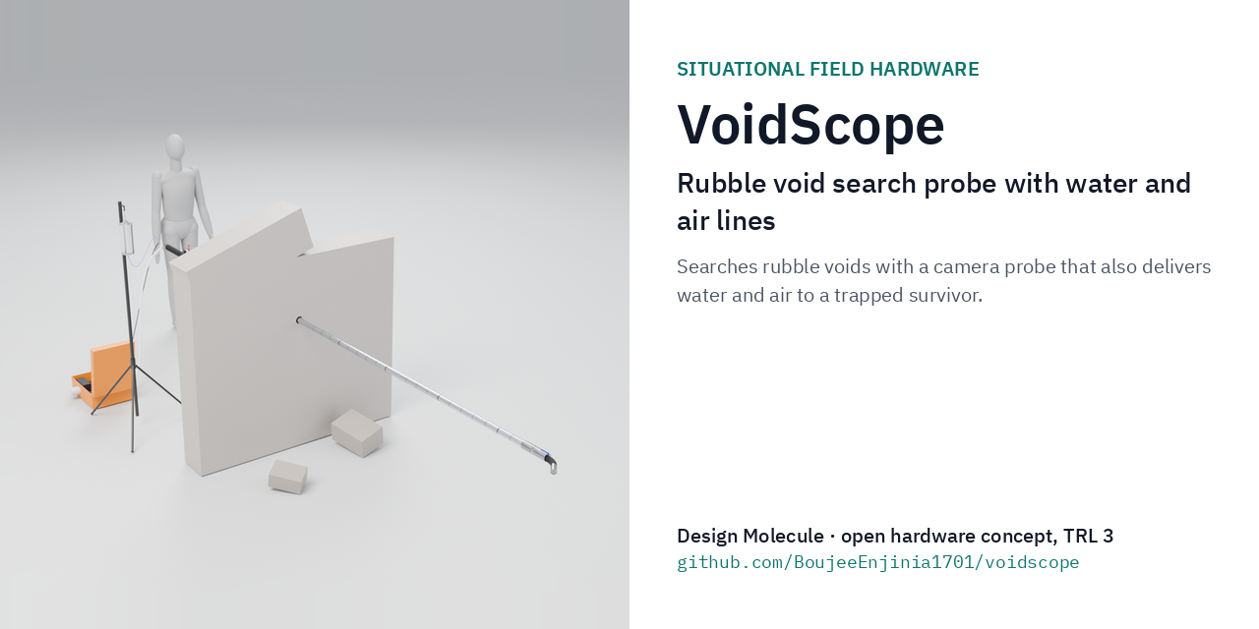
media/social-preview.png
