BoujeeEnjinia1701/voidscope/cad/drawings/VDS-DWG-107.pdf

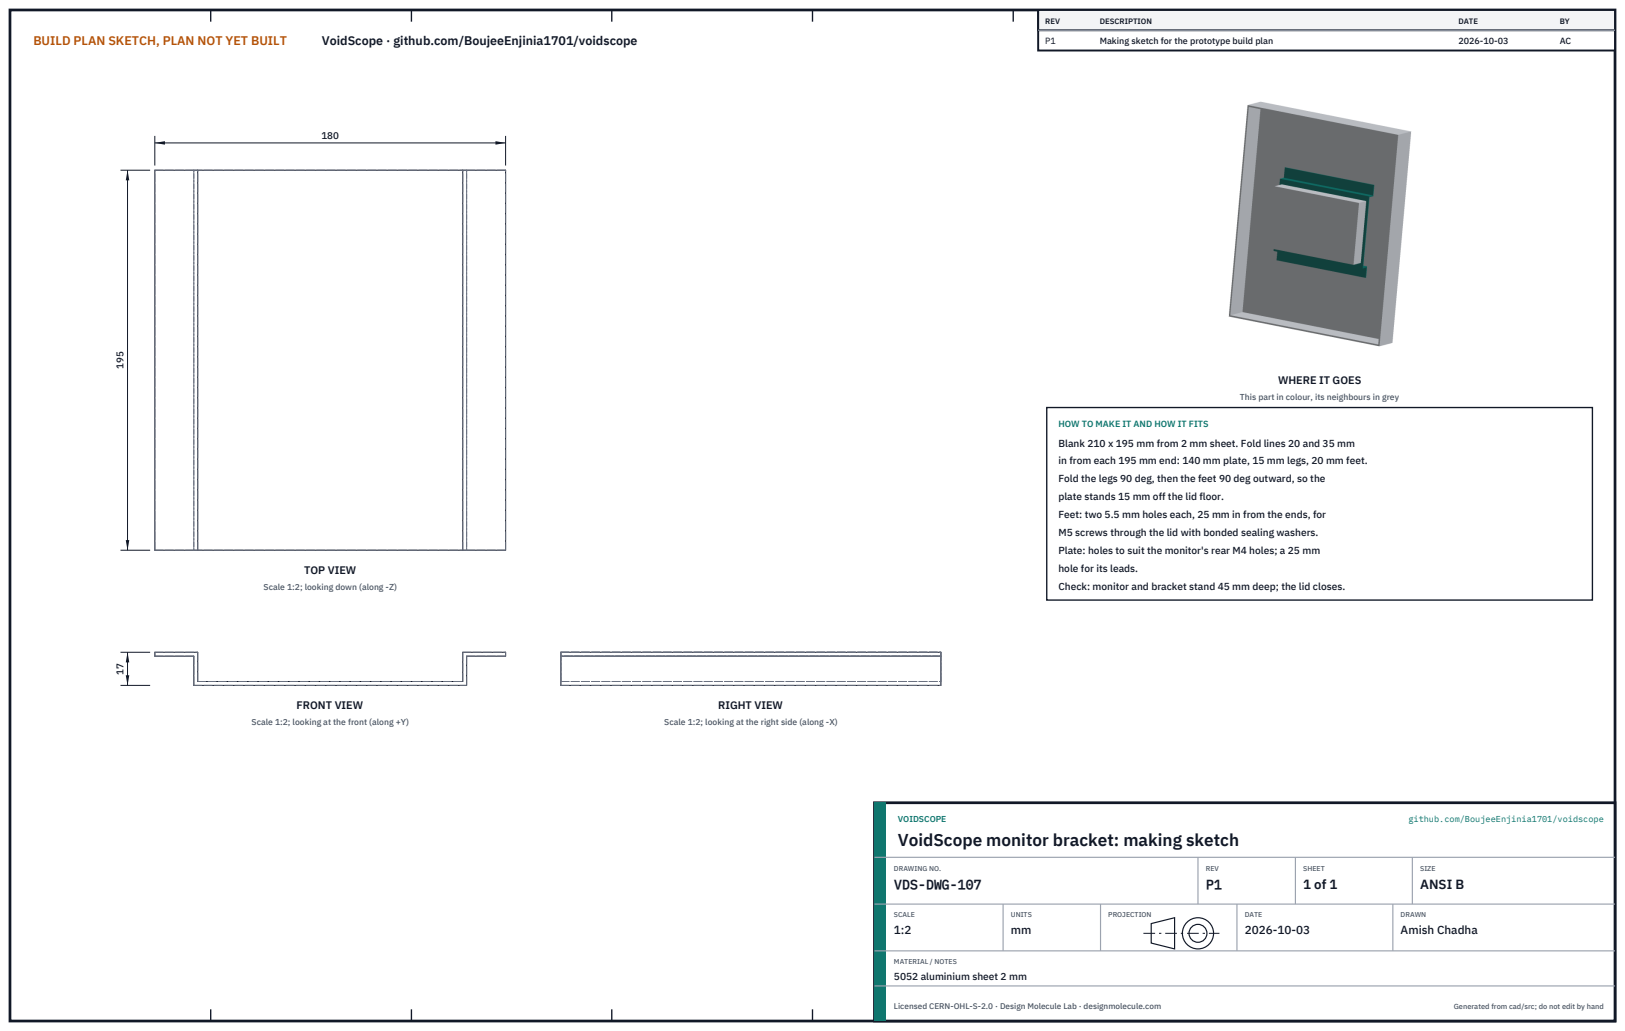
[picture p81: page 1]
BUILD PLAN SKETCH, PLAN NOT YET BUILT; VoidScope · github.com/BoujeeEnjinia1701/voidscope; FRONT VIEW; TOP VIEW; RIGHT VIEW; REV; DESCRIPTION; DATE; Making sketch for the prototype build plan; VOIDSCOPE; github.com/BoujeeEnjinia1701/voidscope; DRAWING NO. VDS-DWG-107; REV P1; SHEET 1 of 1; SIZE ANSI B; SCALE 1:2; UNITS mm; PROJECTION; DRAWN Amish Chadha; Licensed CERN-OHL-S-2.0 · Design Molecule Lab · designmolecule.com; Generated from cad/src; do not edit by hand

WHERE IT GOES

This part in colour, its neighbours in grey

HOW TO MAKE IT AND HOW IT FITS
Blank 210 x 195 mm from 2 mm sheet. Fold lines 20 and 35 mm
in from each 195 mm end: 140 mm plate, 15 mm legs, 20 mm feet.
Fold the legs 90 deg, then the feet 90 deg outward, so the
plate stands 15 mm off the lid floor.
Feet: two 5.5 mm holes each, 25 mm in from the ends, for
M5 screws through the lid with bonded sealing washers.
Plate: holes to suit the monitor's rear M4 holes; a 25 mm
hole for its leads.
Check: monitor and bracket stand 45 mm deep; the lid closes.

Scale 1:2; looking down (along -Z)

Scale 1:2; looking at the front (along +Y)

Scale 1:2; looking at the right side (along -X)

VoidScope monitor bracket: making sketch

MATERIAL / NOTES
5052 aluminium sheet 2 mm
