BoujeeEnjinia1701/voidscope/cad/drawings/VDS-DWG-109.pdf

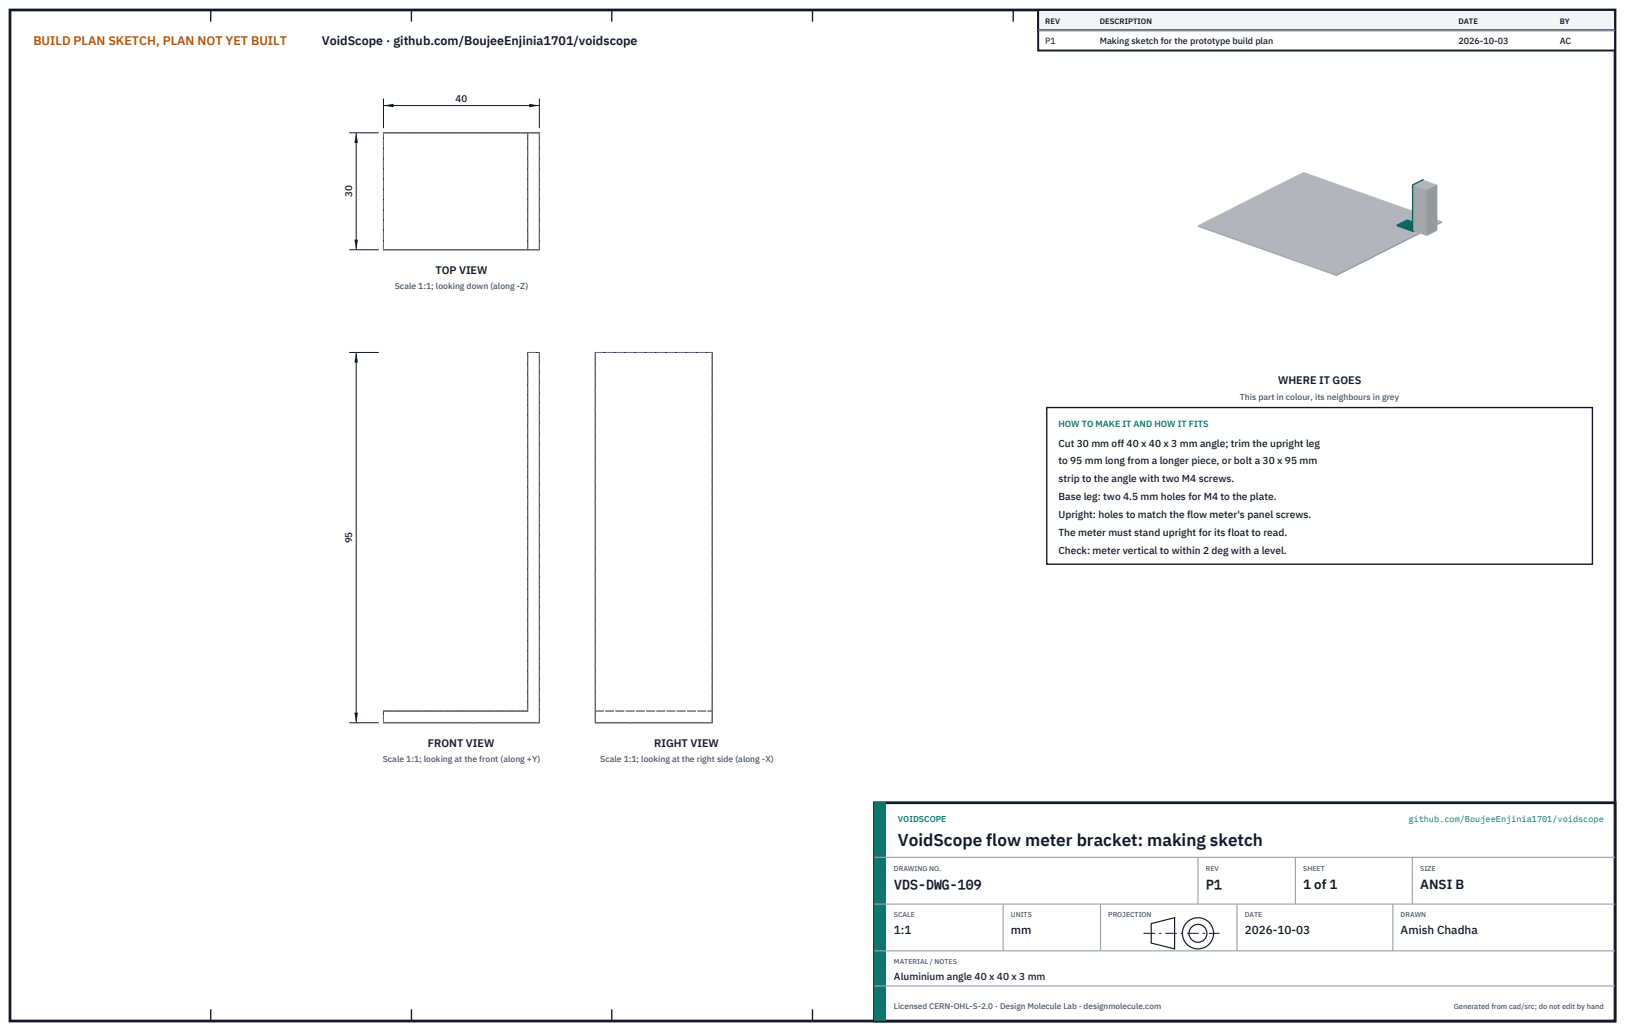
[picture p82: page 1]
BUILD PLAN SKETCH, PLAN NOT YET BUILT; VoidScope · github.com/BoujeeEnjinia1701/voidscope; FRONT VIEW; TOP VIEW; RIGHT VIEW; REV; DESCRIPTION; DATE; Making sketch for the prototype build plan; VOIDSCOPE; github.com/BoujeeEnjinia1701/voidscope; DRAWING NO. VDS-DWG-109; REV P1; SHEET 1 of 1; SIZE ANSI B; SCALE 1:1; UNITS mm; PROJECTION; DRAWN Amish Chadha; Licensed CERN-OHL-S-2.0 · Design Molecule Lab · designmolecule.com; Generated from cad/src; do not edit by hand

Scale 1:1; looking down (along -Z)

WHERE IT GOES

This part in colour, its neighbours in grey

HOW TO MAKE IT AND HOW IT FITS
Cut 30 mm off 40 x 40 x 3 mm angle; trim the upright leg
to 95 mm long from a longer piece, or bolt a 30 x 95 mm
strip to the angle with two M4 screws.
Base leg: two 4.5 mm holes for M4 to the plate.
Upright: holes to match the flow meter's panel screws.
The meter must stand upright for its float to read.
Check: meter vertical to within 2 deg with a level.

Scale 1:1; looking at the front (along +Y)

Scale 1:1; looking at the right side (along -X)

VoidScope flow meter bracket: making sketch

MATERIAL / NOTES
Aluminium angle 40 x 40 x 3 mm
